chdsbd/rpi-lock/unlock_door.py

#!/usr/bin/env python
from __future__ import print_function

import RPi.GPIO as GPIO
import time
import socket
import os
try:
    import configparser
except ImportError:
    import ConfigParser as configparser

# Default values
frequency = 50 # Hz
servo_pin = 27
duty_cycle_open, duty_cycle_closed = 6, 3  # in %

config_file_paths = [os.path.expanduser('~/rpi-lock.cfg'),
                     os.path.join(os.path.realpath(os.path.dirname(__file__)), "rpi-lock.cfg")]
config = configparser.ConfigParser()
config.read(config_file_paths)
try:
    duty_cycle_open = config.getint("SERVO", "OPEN")
    duty_cycle_closed = config.getint("SERVO", "CLOSED")
    servo_pin = config.getint("SERVO", "PIN")
    frequency = config.getint("SERVO", "FREQUENCY")
except configparser.Error as e:
    print("ConfigParser Error: ", e)

GPIO.setmode(GPIO.BCM)
GPIO.setup(servo_pin, GPIO.OUT)

servo = GPIO.PWM(servo_pin, frequency)

def server():
    s = socket.socket(socket.AF_INET, socket.SOCK_STREAM)
    s.bind(('localhost', 5555))

    while True:
        s.listen(1)
        conn, addr = s.accept()
        message = conn.recv(1024)
        print("Recieved request: ", message.decode("utf-8"))
        if message == b"unlock":
            unlock_door()
            conn.sendall(b"Servo Triggered")
        else:
            conn.sendall(b"Improper request, not unlocking door.")


def unlock_door():
    print('Unlocking...')
    servo.start(duty_cycle_open)
    time.sleep(2.5)
    print('Locking...')
    servo.ChangeDutyCycle(duty_cycle_closed)
    time.sleep(1)
    servo.ChangeDutyCycle(0)

if __name__ == '__main__':
    try:
        server()
    except KeyboardInterrupt:
        GPIO.cleanup()
    except:
        GPIO.cleanup()
